rkeen9/Bert-Slime-PCB/images/charger_only.jpg

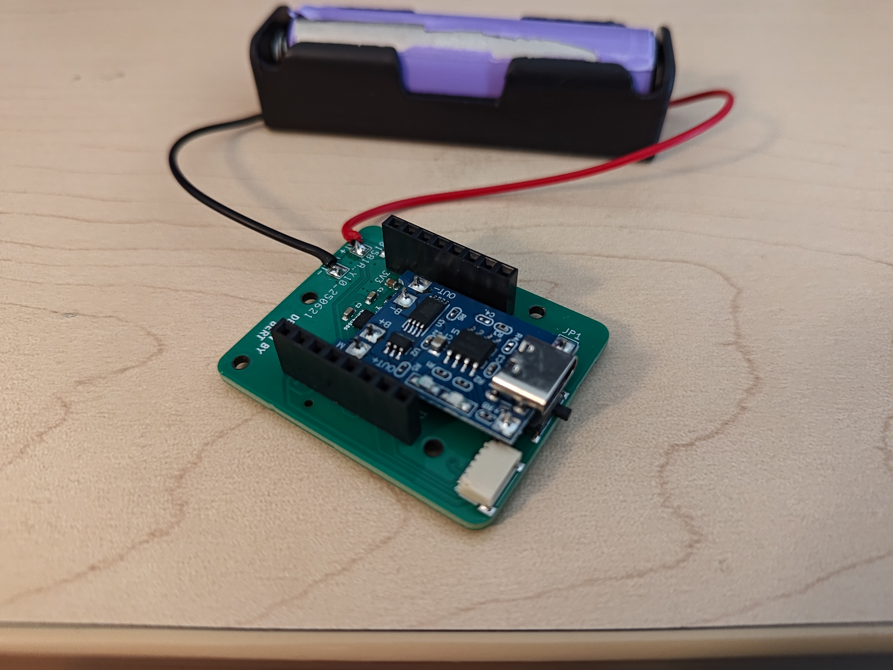
images/charger_only.jpg
