rkeen9/Bert-Slime-PCB/images/PCB-Layout.png

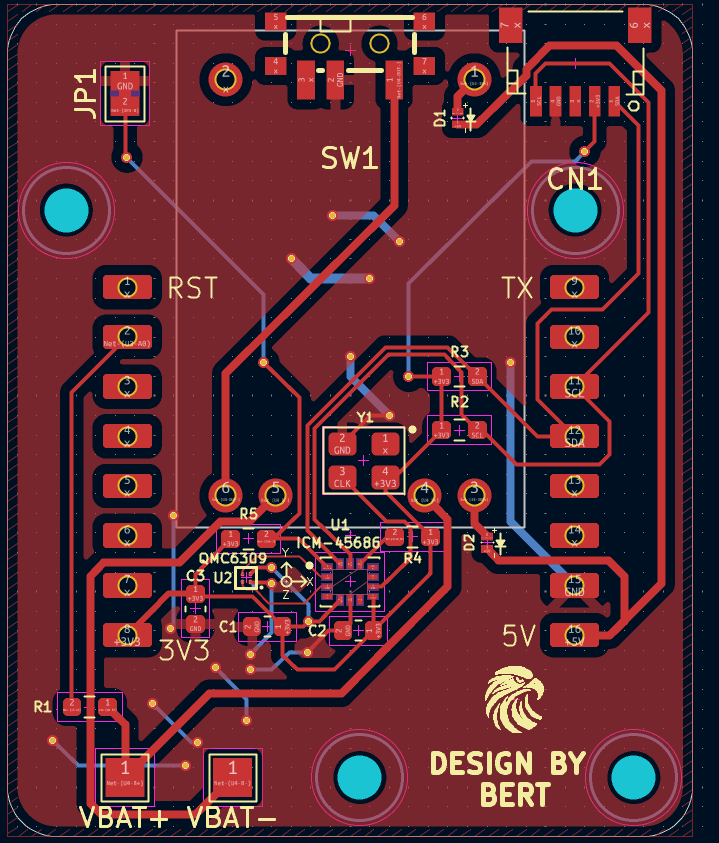
images/PCB-Layout.png
