rkeen9/Bert-Slime-PCB/images/pcb_only.jpg

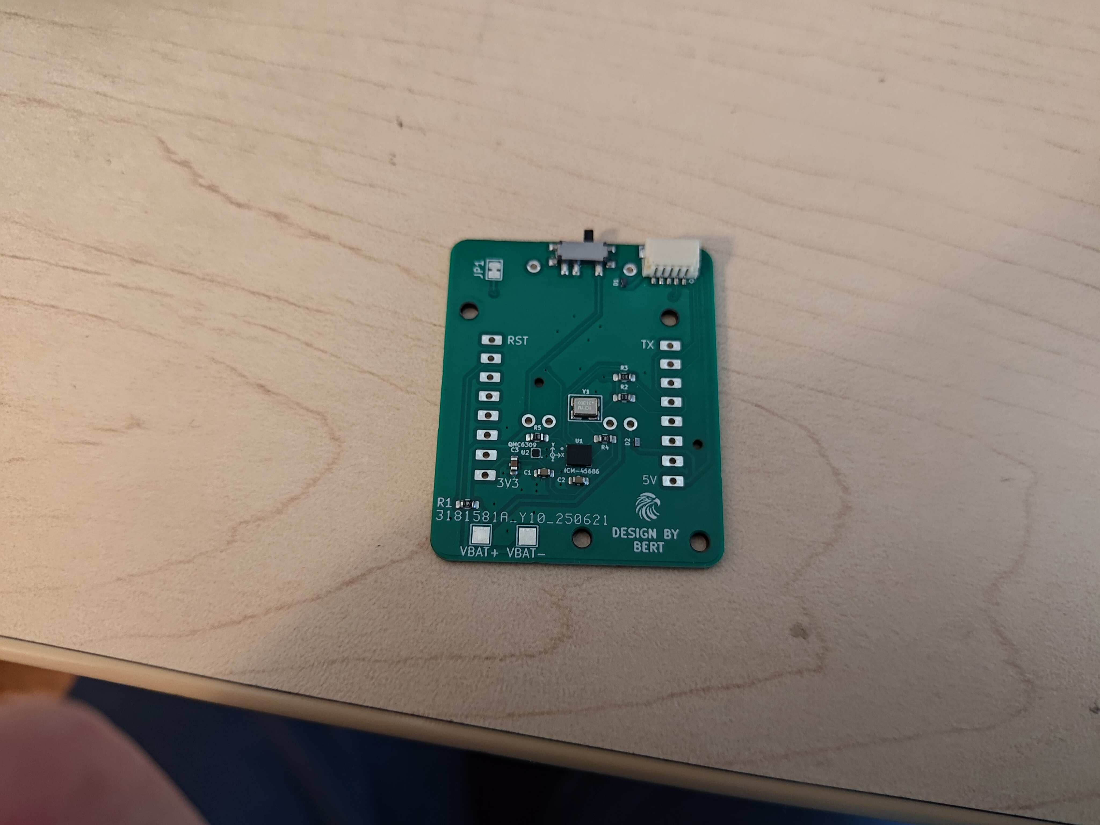
images/pcb_only.jpg
