rkeen9/Bert-Slime-PCB/images/X-Ray/1.jpg

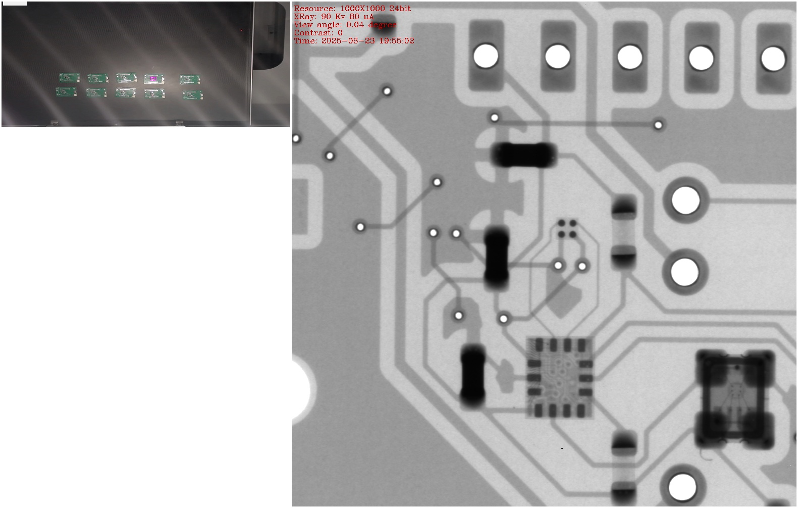
images/X-Ray/1.jpg
