rkeen9/Bert-Slime-PCB/images/X-Ray/2.jpg

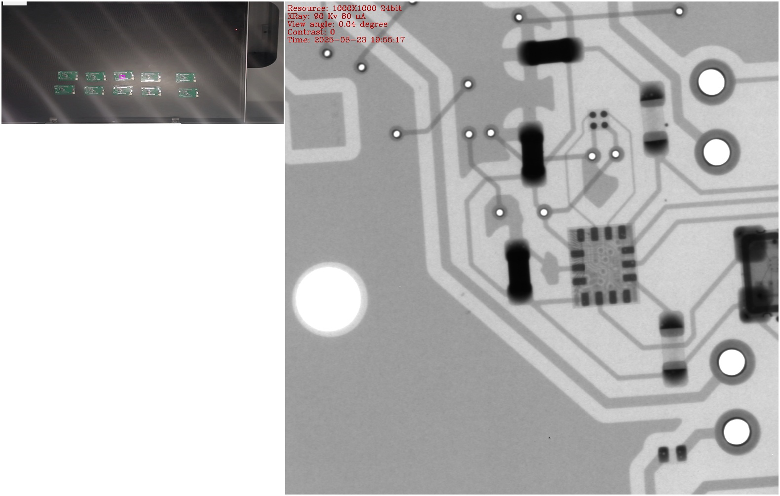
images/X-Ray/2.jpg
