rkeen9/Bert-Slime-PCB/images/X-Ray/3.jpg

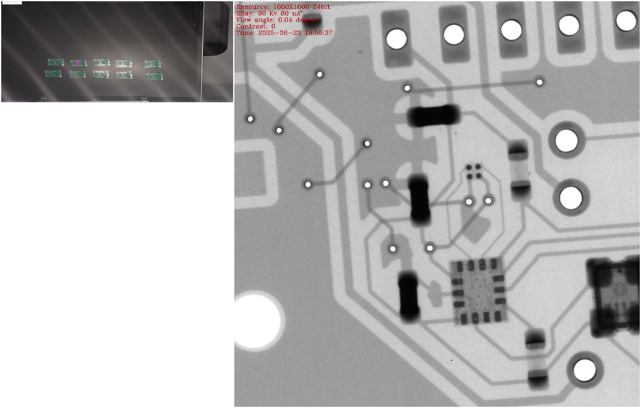
images/X-Ray/3.jpg
