rkeen9/Bert-Slime-PCB/images/X-Ray/4.jpg

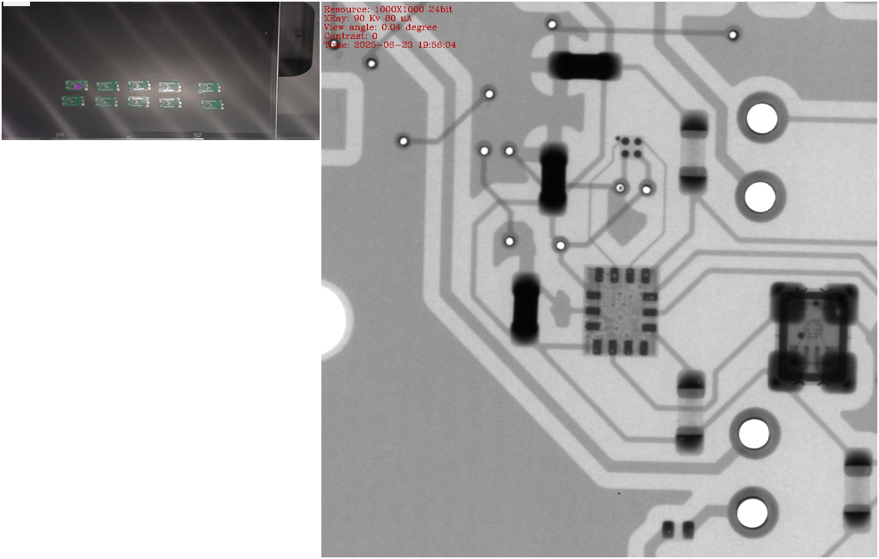
images/X-Ray/4.jpg
