rkeen9/Bert-Slime-PCB/images/X-Ray/5.jpg

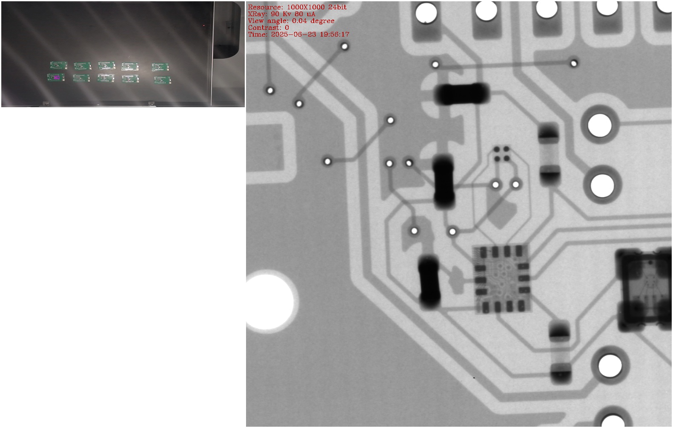
images/X-Ray/5.jpg
