rkeen9/Bert-Slime-PCB/images/X-Ray/6.jpg

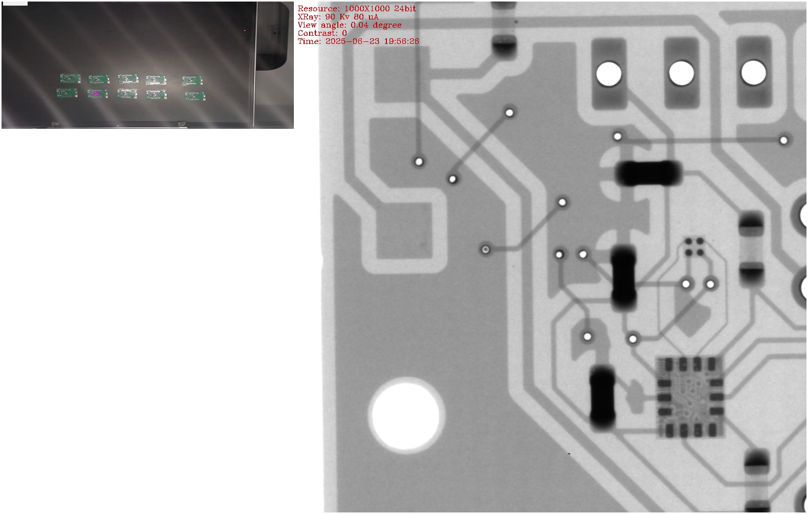
images/X-Ray/6.jpg
