rkeen9/Bert-Slime-PCB/images/X-Ray/7.jpg

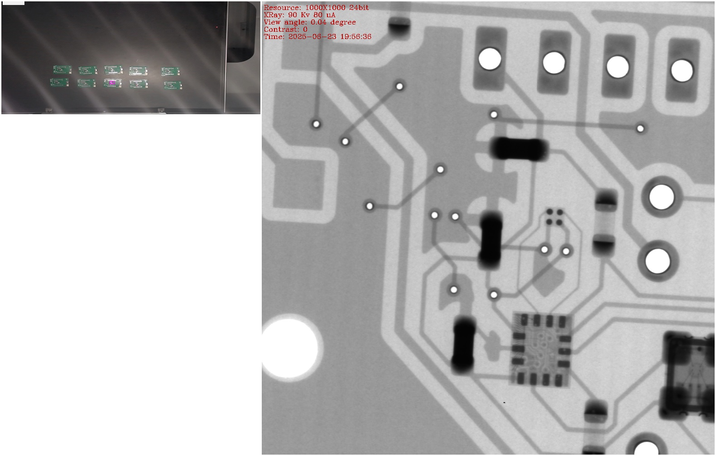
images/X-Ray/7.jpg
