rkeen9/Bert-Slime-PCB/images/X-Ray/8.jpg

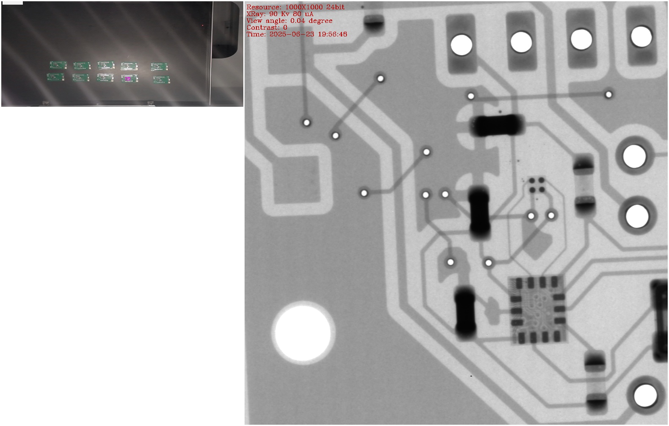
images/X-Ray/8.jpg
