rkeen9/Bert-Slime-PCB/Troubleshooting/temperature_formula.png

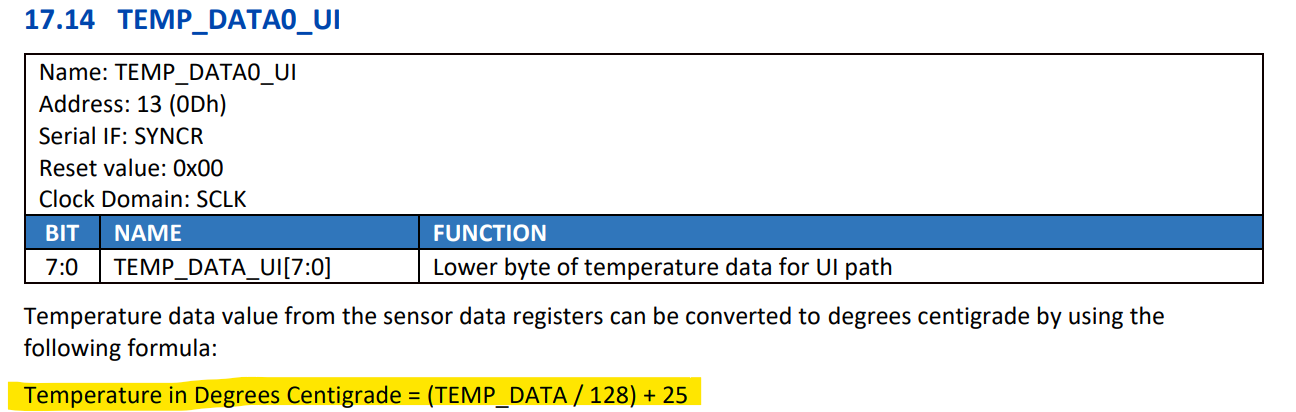
Troubleshooting/temperature_formula.png
